dtheriault/RptrIDer/Pics/IMG_0759.JPG

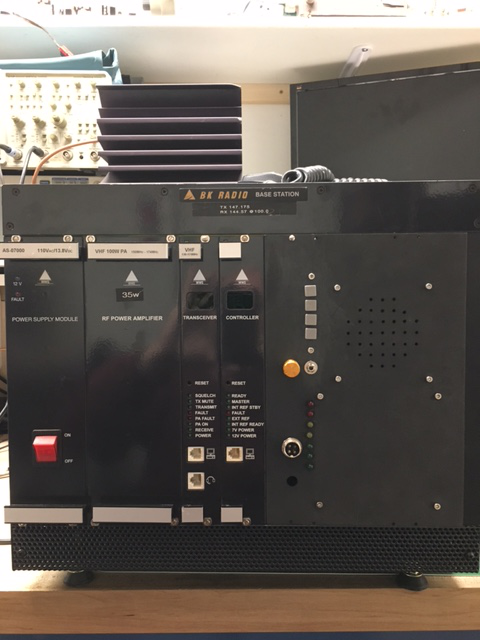
Pics/IMG_0759.JPG
