dtheriault/RptrIDer/Pics/IMG_0760.JPG

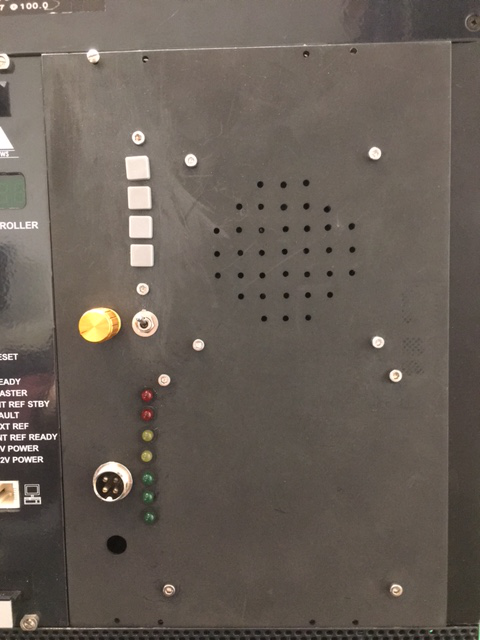
Pics/IMG_0760.JPG
