dtheriault/RptrIDer/Pics/IMG_0761.JPG

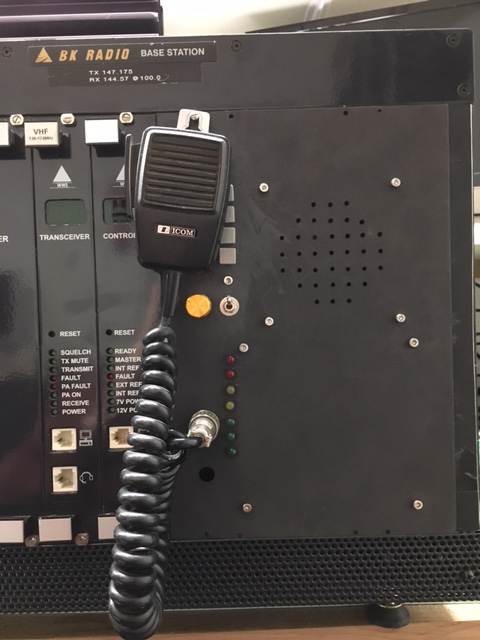
Pics/IMG_0761.JPG
