dtheriault/RptrIDer/Pics/IMG_0763.JPG

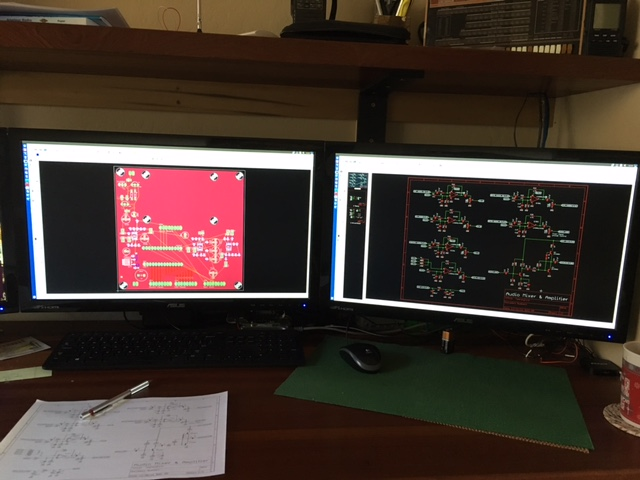
Pics/IMG_0763.JPG
