dtheriault/RptrIDer/Pics/IMG_0766.JPG

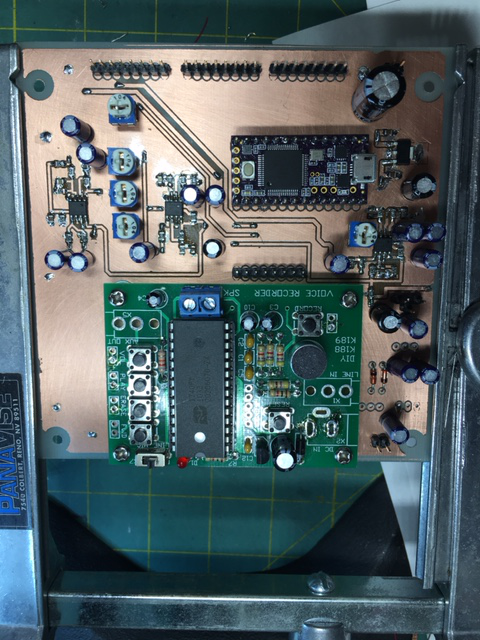
Pics/IMG_0766.JPG
