dtheriault/RptrIDer/Pics/P2020009.JPG

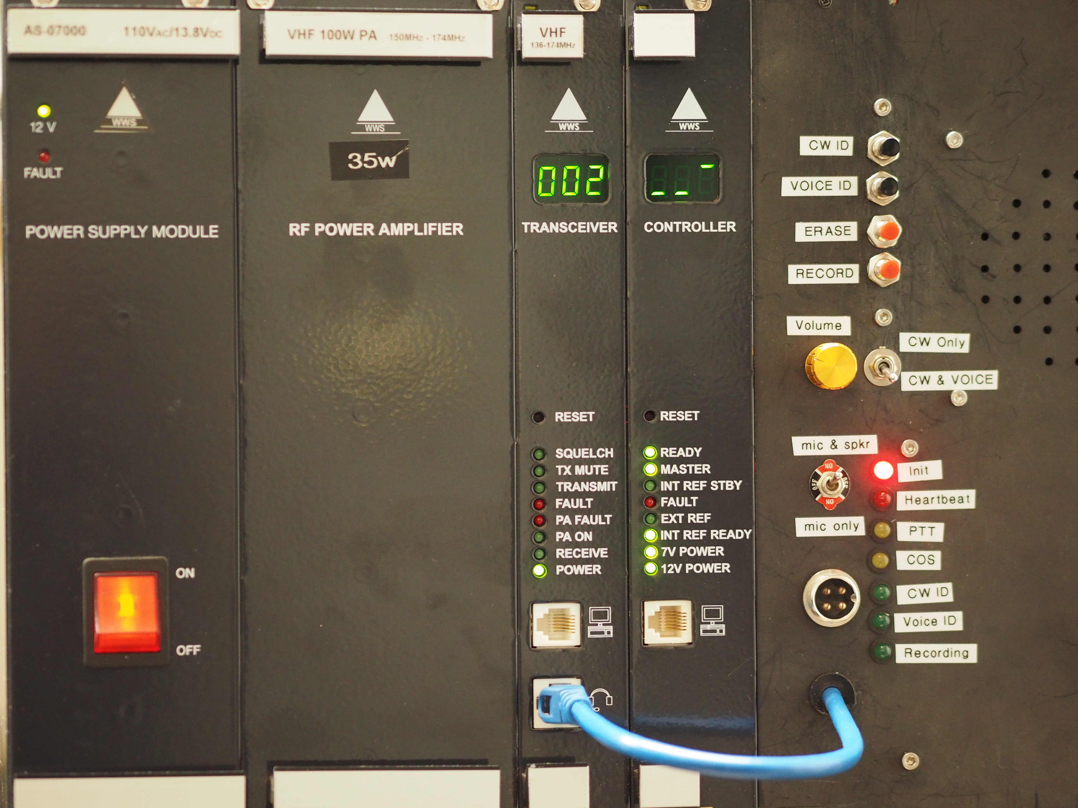
Pics/P2020009.JPG
